Nada-Khafagy/Robotics_project/right_arm/pics/Block_diagram_part2.png

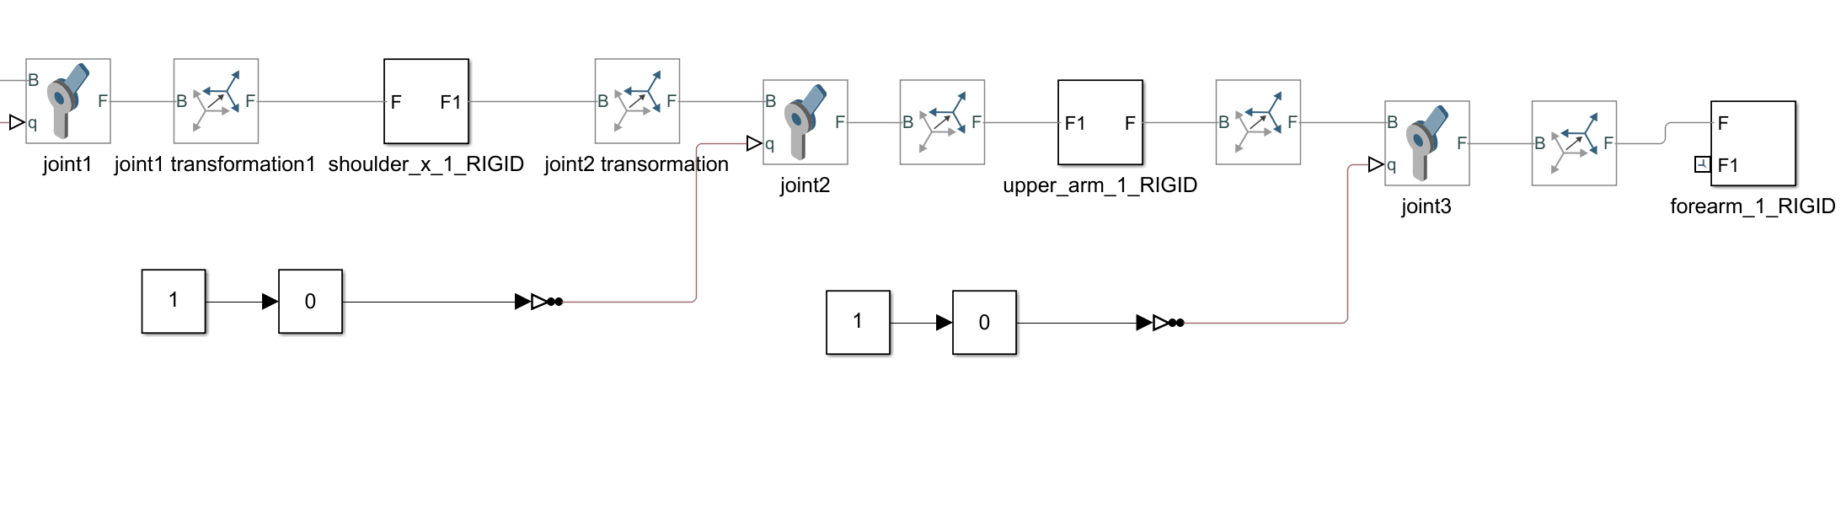
right_arm/pics/Block_diagram_part2.png
