Nada-Khafagy/Robotics_project/RightLeftArms/fig/block Diagram.png

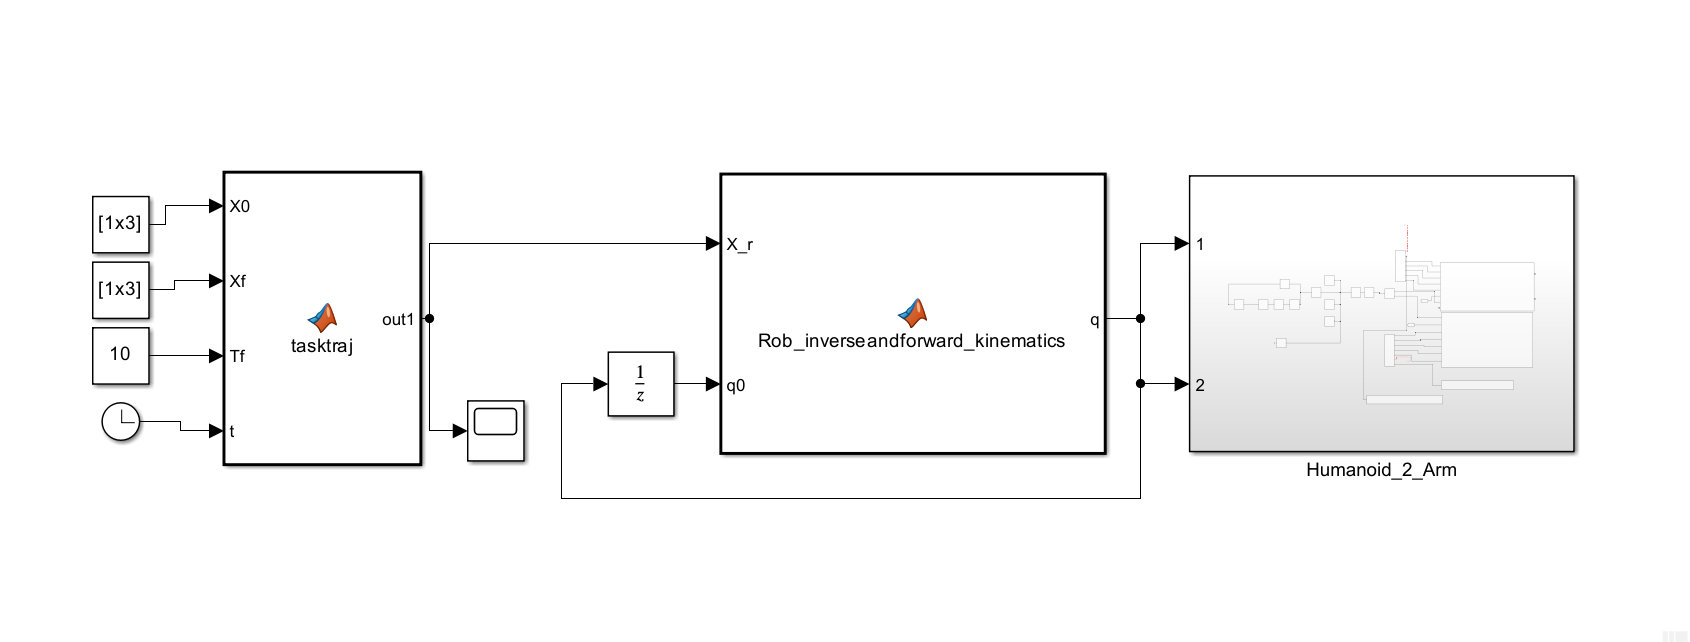
RightLeftArms/fig/block Diagram.png
