Nada-Khafagy/Robotics_project/RightLeftArms/Simscape_files_updated/forearm_MX-28-right_sldprt.STEP

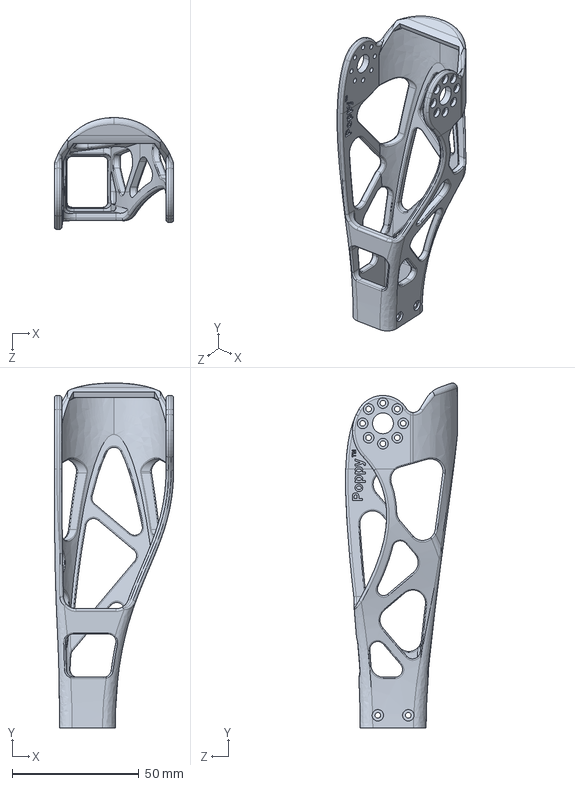
[picture p36: CAD file, 2023-10-06]
RightLeftArms/Simscape_files_updated/forearm_MX-28-right_sldprt.STEP
47.0 x 135.9 x 44.1 mm
