Nada-Khafagy/Robotics_project/RightLeftArms/Simscape_files_updated/HN07-N101_Défaut_sldprt.STEP

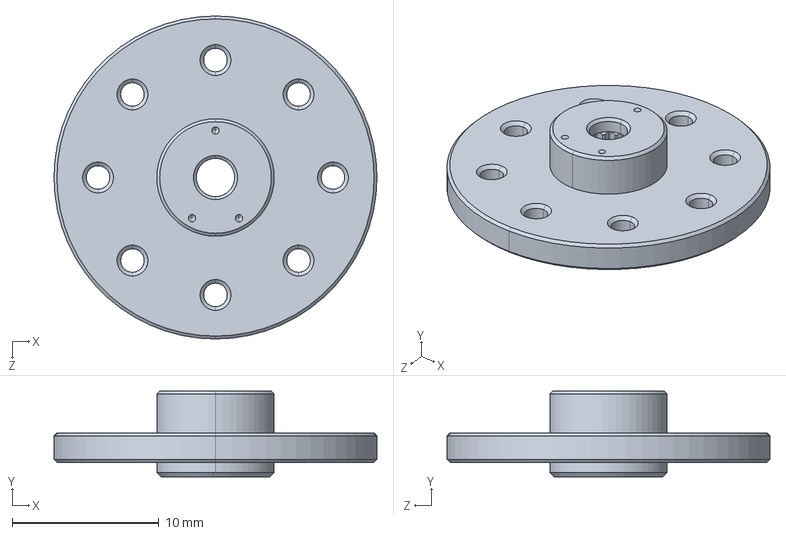
[picture p37: CAD file, 2023-10-06]
RightLeftArms/Simscape_files_updated/HN07-N101_Défaut_sldprt.STEP
22.0 x 5.85 x 22.0 mm
