Nada-Khafagy/Robotics_project/right_arm/Arduino_code/Milestone4/Milestone4.ino

#include <dummy.h>


#include <Servo.h>

Servo motor1;
Servo motor2;
Servo motor3;
Servo motor4;

int q0_ref = 90;
int q1_ref = 0;
int q2_ref = 90;
int q3_ref = 90;

int pos = 0;
int size;
int q0[] = {50.3488, 53.5317, 56.6565, 59.7375, 62.7849, 65.8062, 68.8061, 71.7873, 74.7499, 77.6925, 80.6116, 83.5016, 86.3558, 89.1658, 91.9220, 94.6144, 97.2325, 99.7662, 102.2059, 104.5433, 106.7714, 108.8848, 110.8798, 112.7539, 114.5064, 116.1374, 117.6480, 119.0400, 120.3153, 121.4765};

int q1[] = {22.4768, 23.9267, 25.3571, 26.7725, 28.1755, 29.5677, 30.9489, 32.3181, 33.6730, 35.0100, 36.3242, 37.6094, 38.8581, 40.0615, 41.2097, 42.2917, 43.2962, 44.2114, 45.0261, 45.7299, 46.3137, 46.7701, 47.0938, 47.2817, 47.3325, 47.2468, 47.0268, 46.6755, 46.1969, 45.5951};

int  q2[] = {24.9068, 24.9917, 25.0894, 25.2031, 25.3360, 25.4921, 25.6755, 25.8909, 26.1432, 26.4373, 26.7787, 27.1723, 27.6230, 28.1350, 28.7116, 29.3551, 30.0659, 30.8431, 31.6835, 32.5823, 33.5328, 34.5272, 35.5562, 36.6101, 37.6793, 38.7541, 39.8257, 40.8860, 41.9280, 42.9456};
int q3[] = {70.0283, 73.8662, 77.4322, 80.7526, 83.8468, 86.7285, 89.4078, 91.8916, 94.1842, 96.2882, 98.2045, 99.9329, 101.4724, 102.8211, 103.9768, 104.9374, 105.7006, 106.2642, 106.6267, 106.7870, 106.7446, 106.4996, 106.0528, 105.4055, 104.5595, 103.5169, 102.2802, 100.8515, 99.2328, 97.4256};


void setup() {

  motor1.attach(11);   // Attach motor1 to pin 9
  motor2.attach(9);  // Attach motor2 to pin 10
  motor3.attach(6);  // Attach motor4 to pin 12
  motor4.attach(10);  // Attach motor3 to pin 9
  Serial.begin(9600);

  

size = sizeof(q1) / sizeof(q1[0]);
Serial.begin(9600);
Serial.print(size);
}
void loop() {
    
    delay(20);

  for(int i = 0 ;i <=size; i++)
  {
      motor1.write(min(q0[i] + q0_ref, 180));
      motor2.write(min(q1[i] + q1_ref, 180));
      motor3.write(min(q2[i] + q2_ref, 180));
      motor4.write(min(q3[i] + q3_ref, 180));
      delay(20);

  }

  for(int j = size-1 ; j>=0 ;j--)
  {
      motor1.write(min(q0[j] + q0_ref, 180));
      motor2.write(min(q1[j] + q1_ref, 180));
      motor3.write(min(q2[j] + q2_ref, 180));
      motor4.write(min(q3[j] + q3_ref, 180));
      delay(50);

  }



}
